Fysek/MidiController/Photos/IMG_20180614_170358.jpg

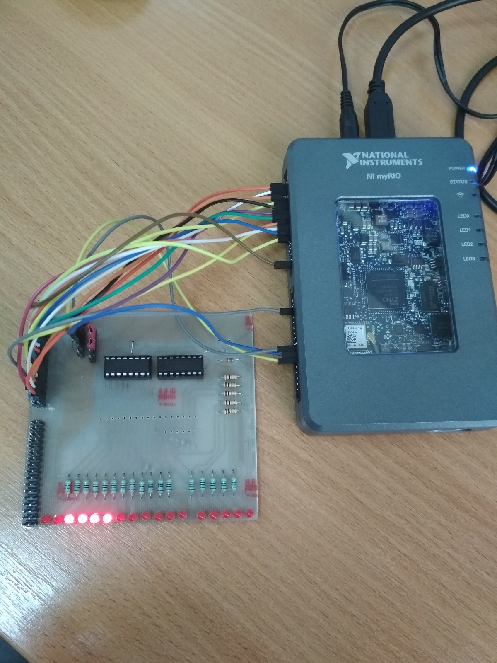
Photos/IMG_20180614_170358.jpg
