Fysek/MidiController/Photos/IMG_20180621_160247.jpg

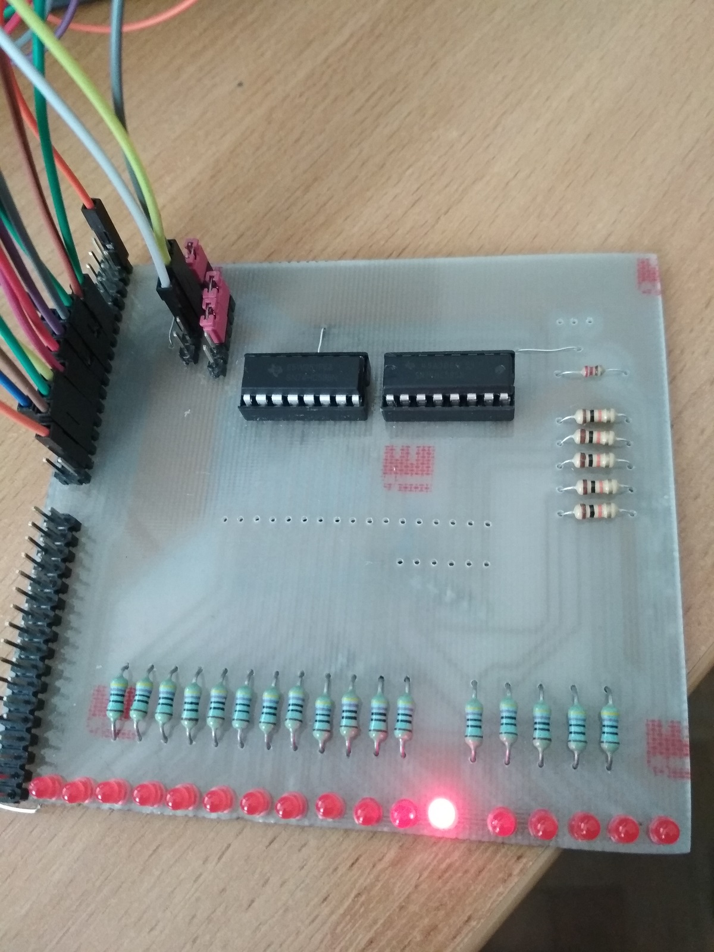
Photos/IMG_20180621_160247.jpg
