Fysek/MidiController/Screen_apps/1.PNG

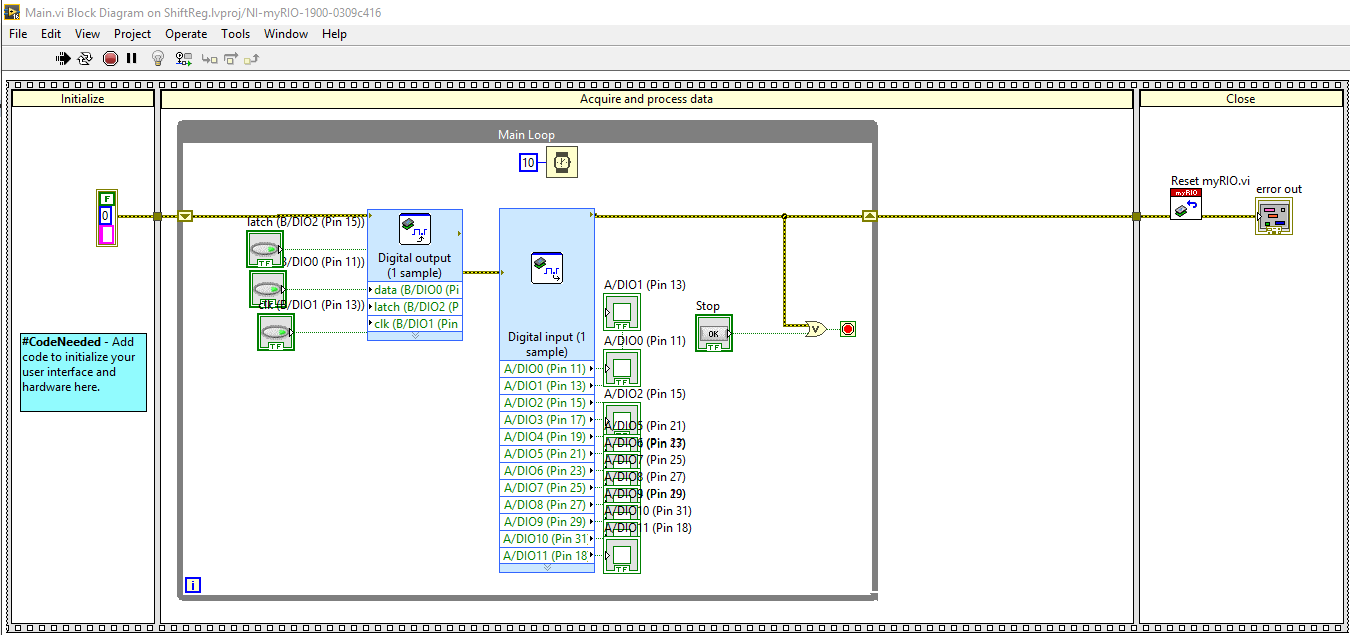
Screen_apps/1.PNG
