Fysek/MidiController/Screen_apps/2.PNG

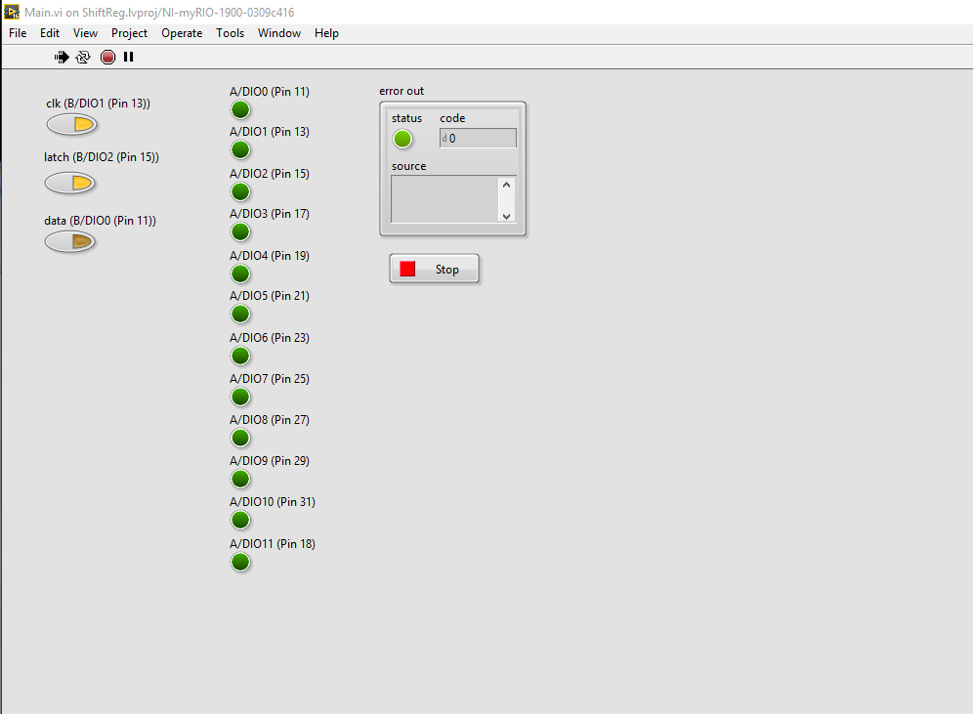
Screen_apps/2.PNG
